vrushikakpanchal/brocode_git/03_project_images/img1.jpg

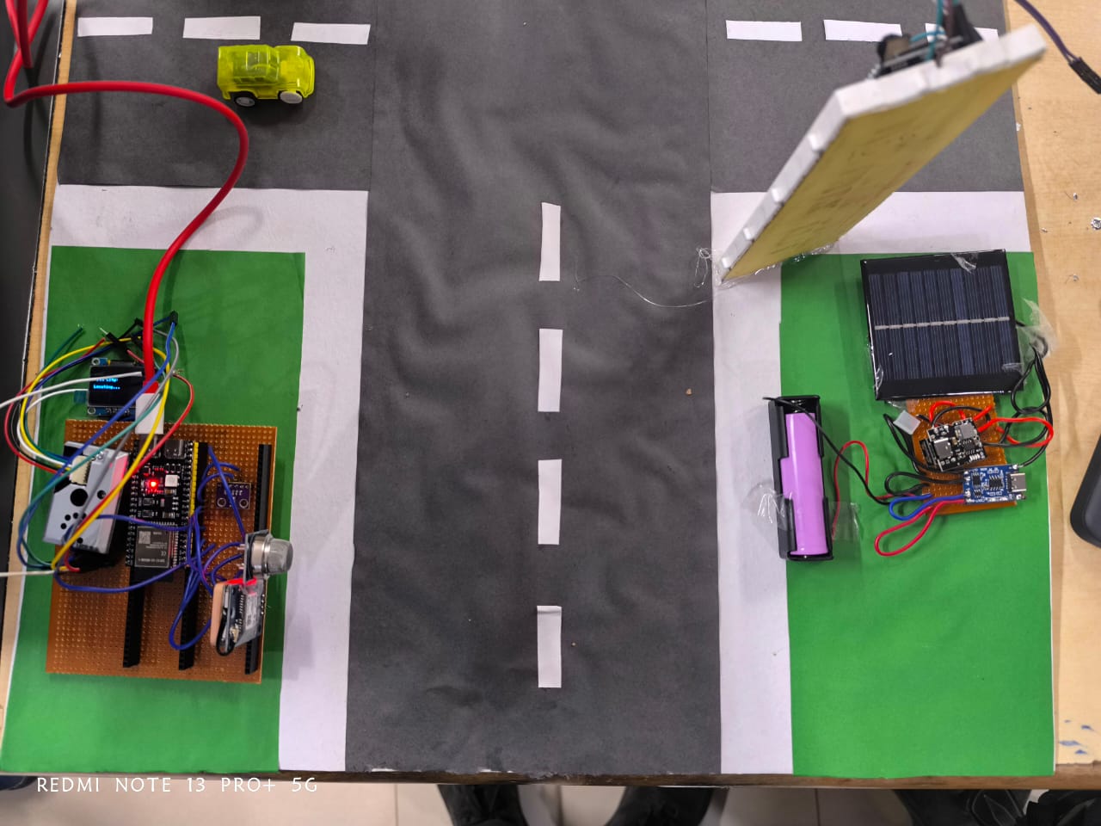
03_project_images/img1.jpg
