vrushikakpanchal/brocode_git/03_project_images/img2.jpg

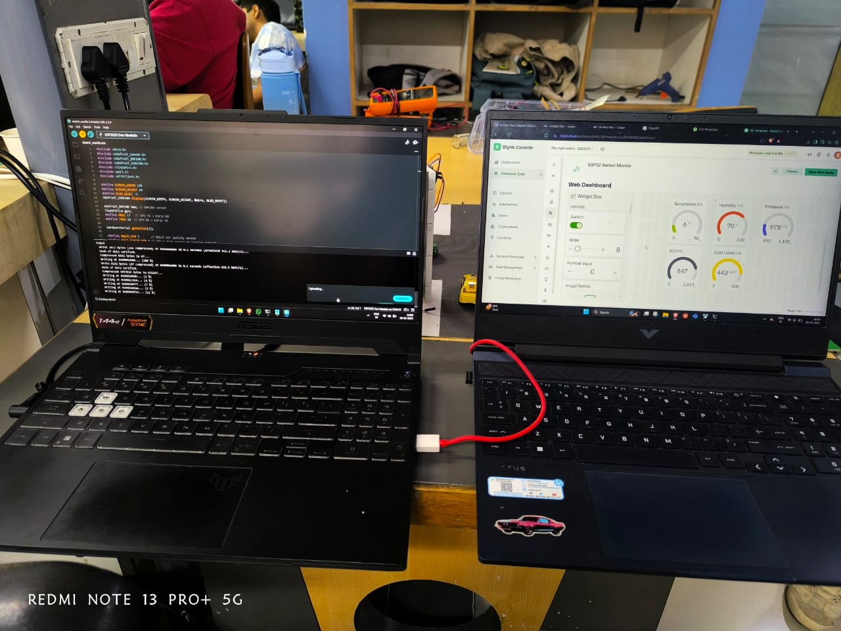
03_project_images/img2.jpg
