vrushikakpanchal/brocode_git/03_project_images/img3.jpg

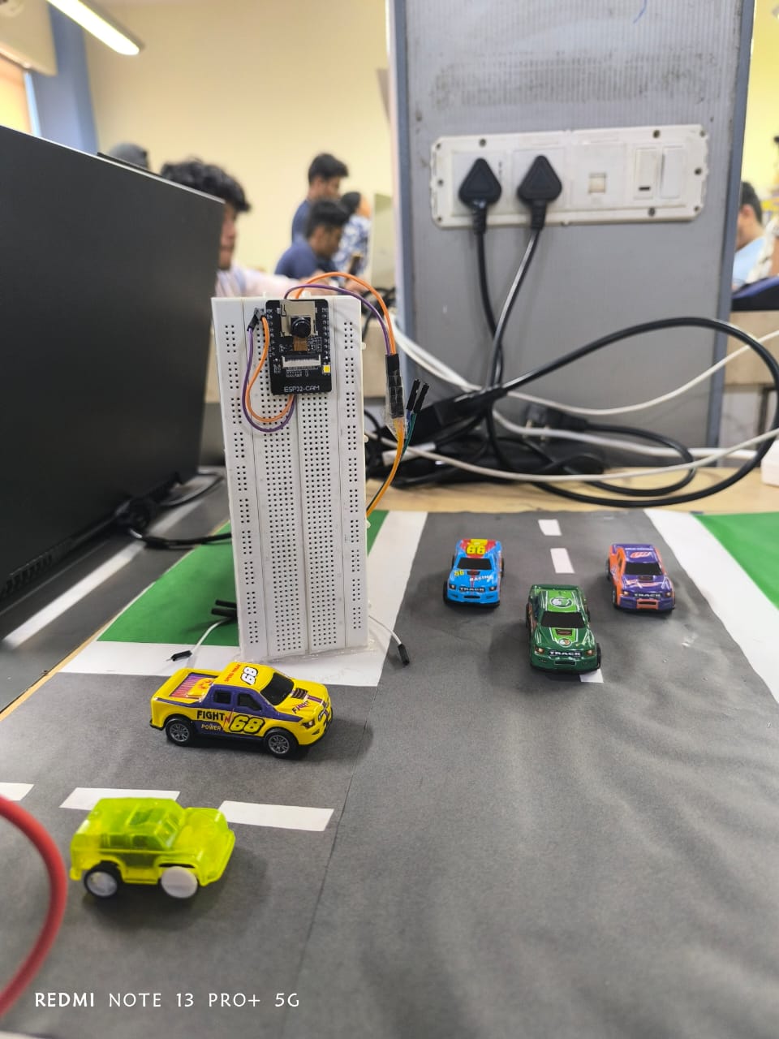
03_project_images/img3.jpg
