vrushikakpanchal/brocode_git/03_project_images/img4.jpg

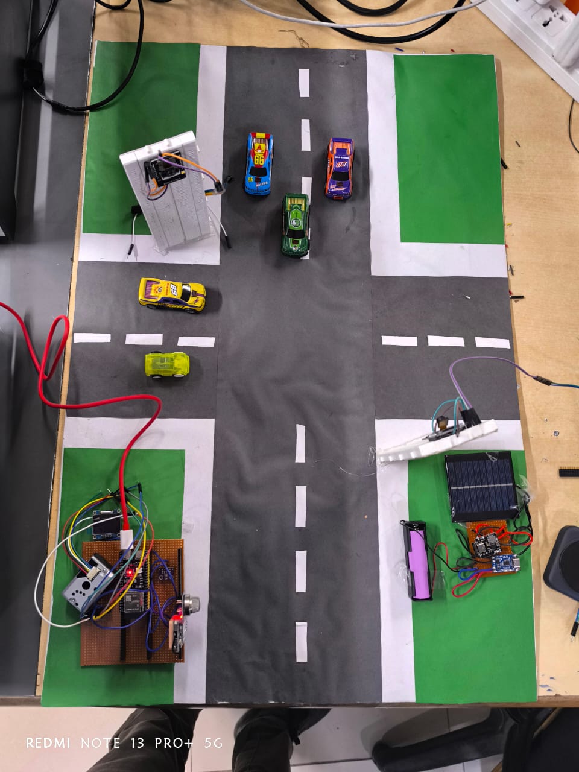
03_project_images/img4.jpg
