vrushikakpanchal/brocode_git/03_project_images/img6.jpg

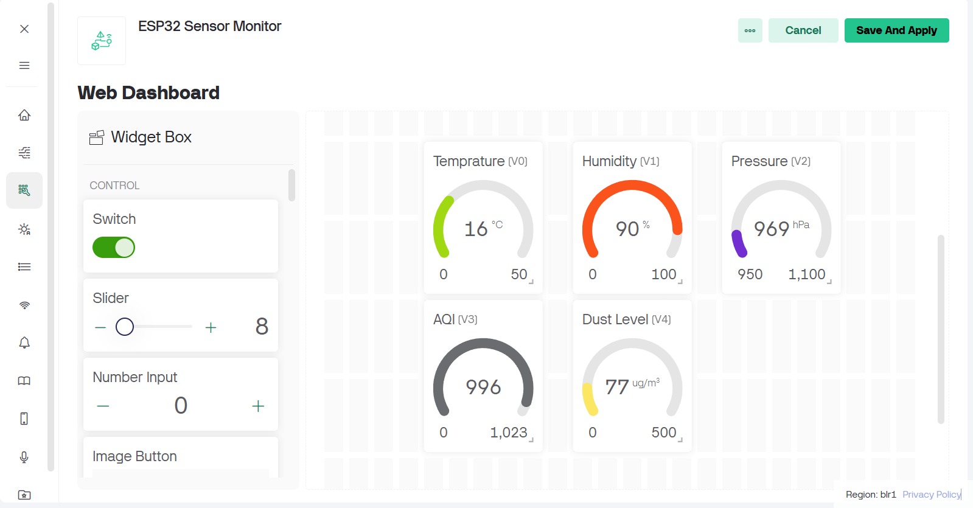
03_project_images/img6.jpg
