vrushikakpanchal/brocode_git/03_project_images/img8.jpg

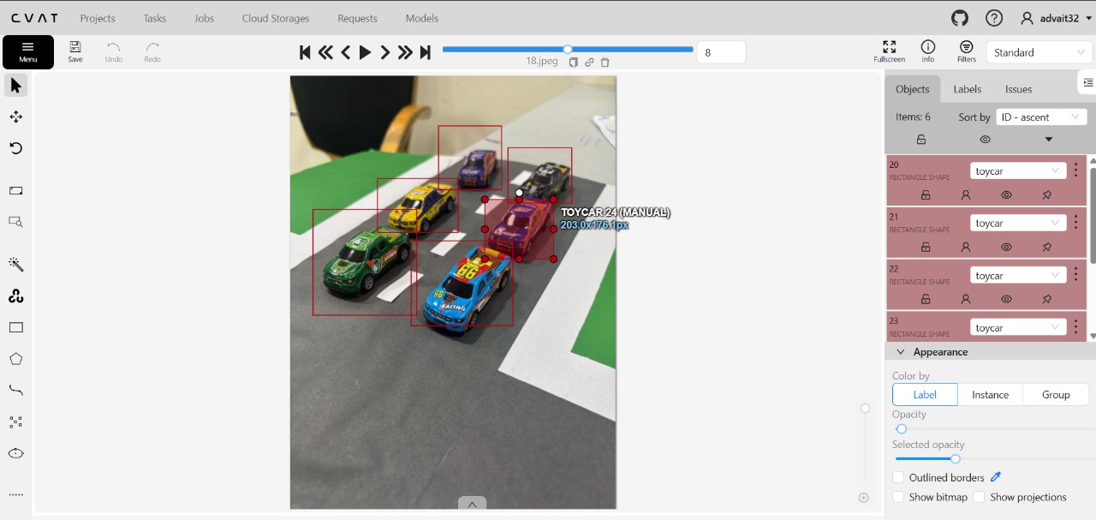
03_project_images/img8.jpg
