vrushikakpanchal/brocode_git/03_project_images/img9.jpg

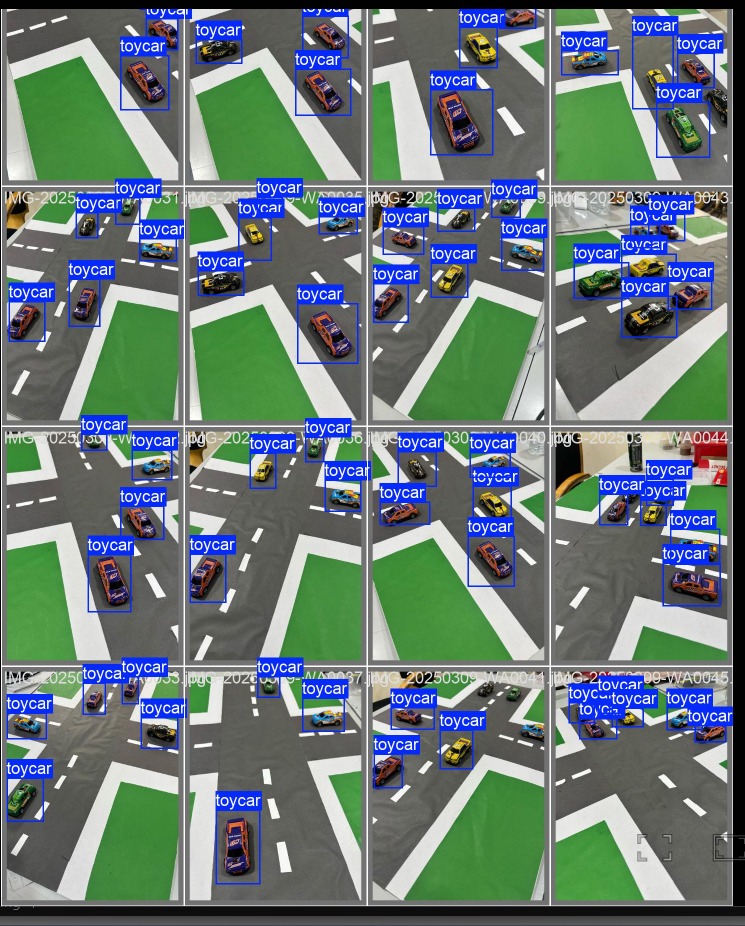
03_project_images/img9.jpg
