vrushikakpanchal/brocode_git/03_project_images/img10.jpg

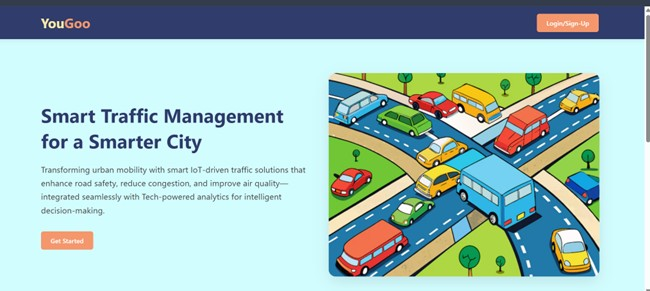
03_project_images/img10.jpg
