vrushikakpanchal/brocode_git/03_project_images/img11.jpg

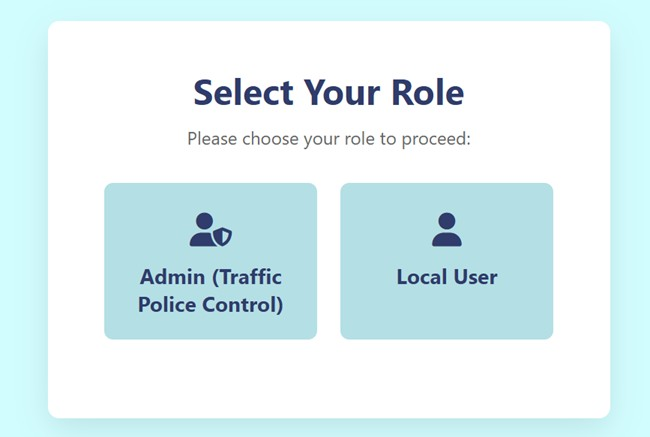
03_project_images/img11.jpg
